poorawsanhsirk/Launch-Party-Badge-Software/assets/IMG_2383.JPG

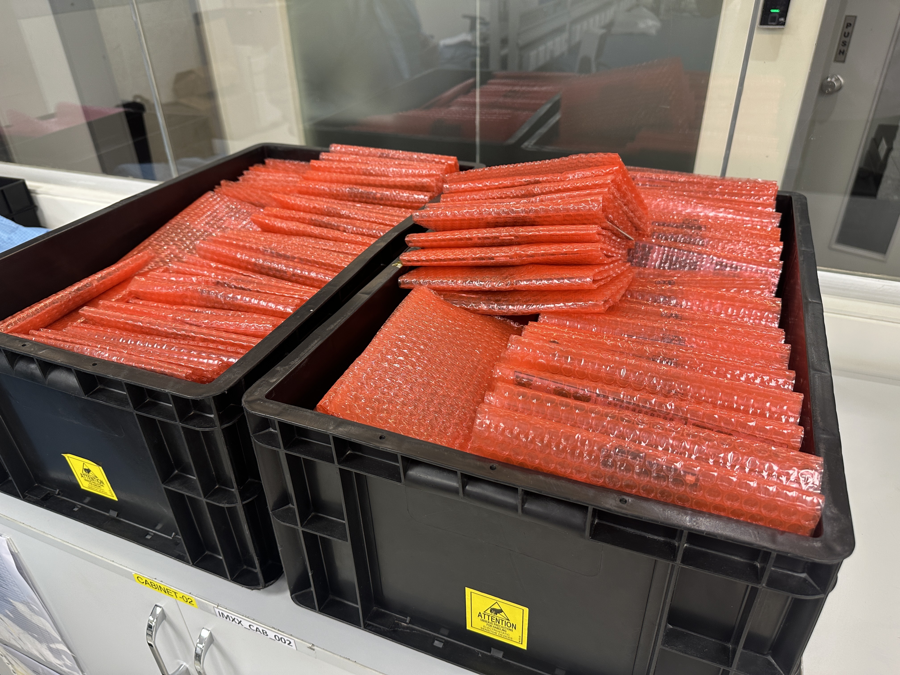
assets/IMG_2383.JPG
