poorawsanhsirk/Launch-Party-Badge-Software/assets/IMG_2390.JPG

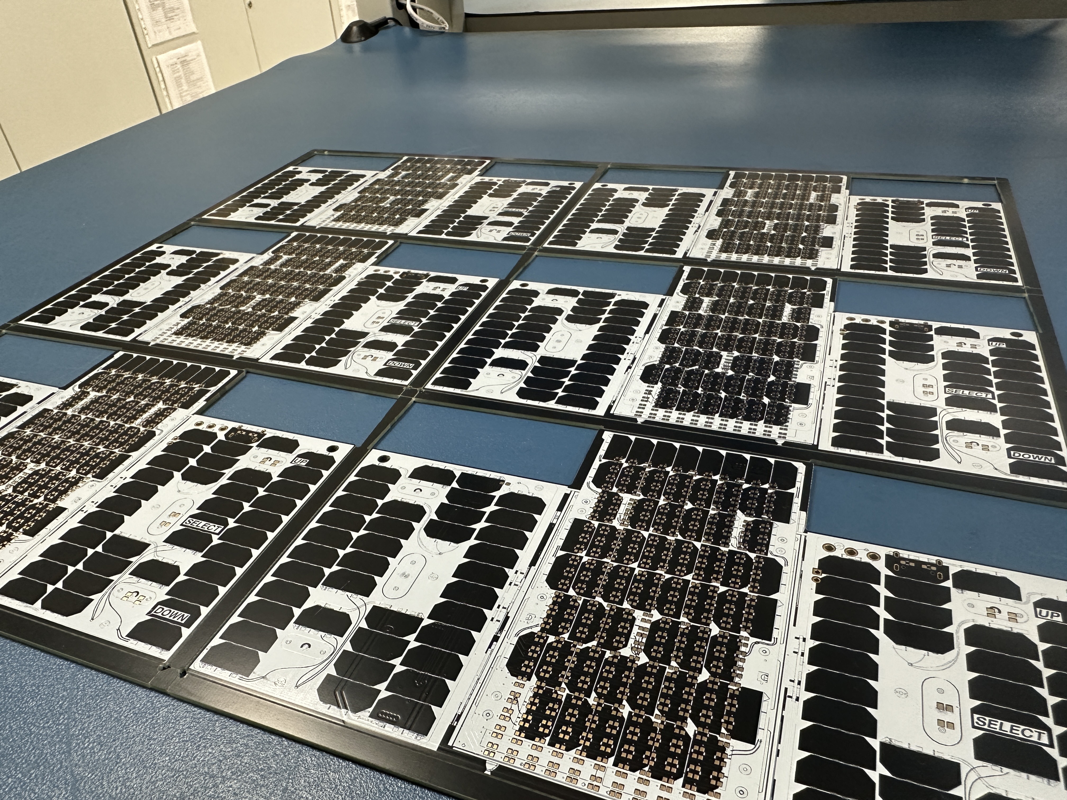
assets/IMG_2390.JPG
