poorawsanhsirk/Launch-Party-Badge-Software/hardware/FF1-LP-Badge/FF1-LP-Badge.kicad_sch

## KiCad design hardware/FF1-LP-Badge/FF1-LP-Badge.kicad_sch (2025-01-15)

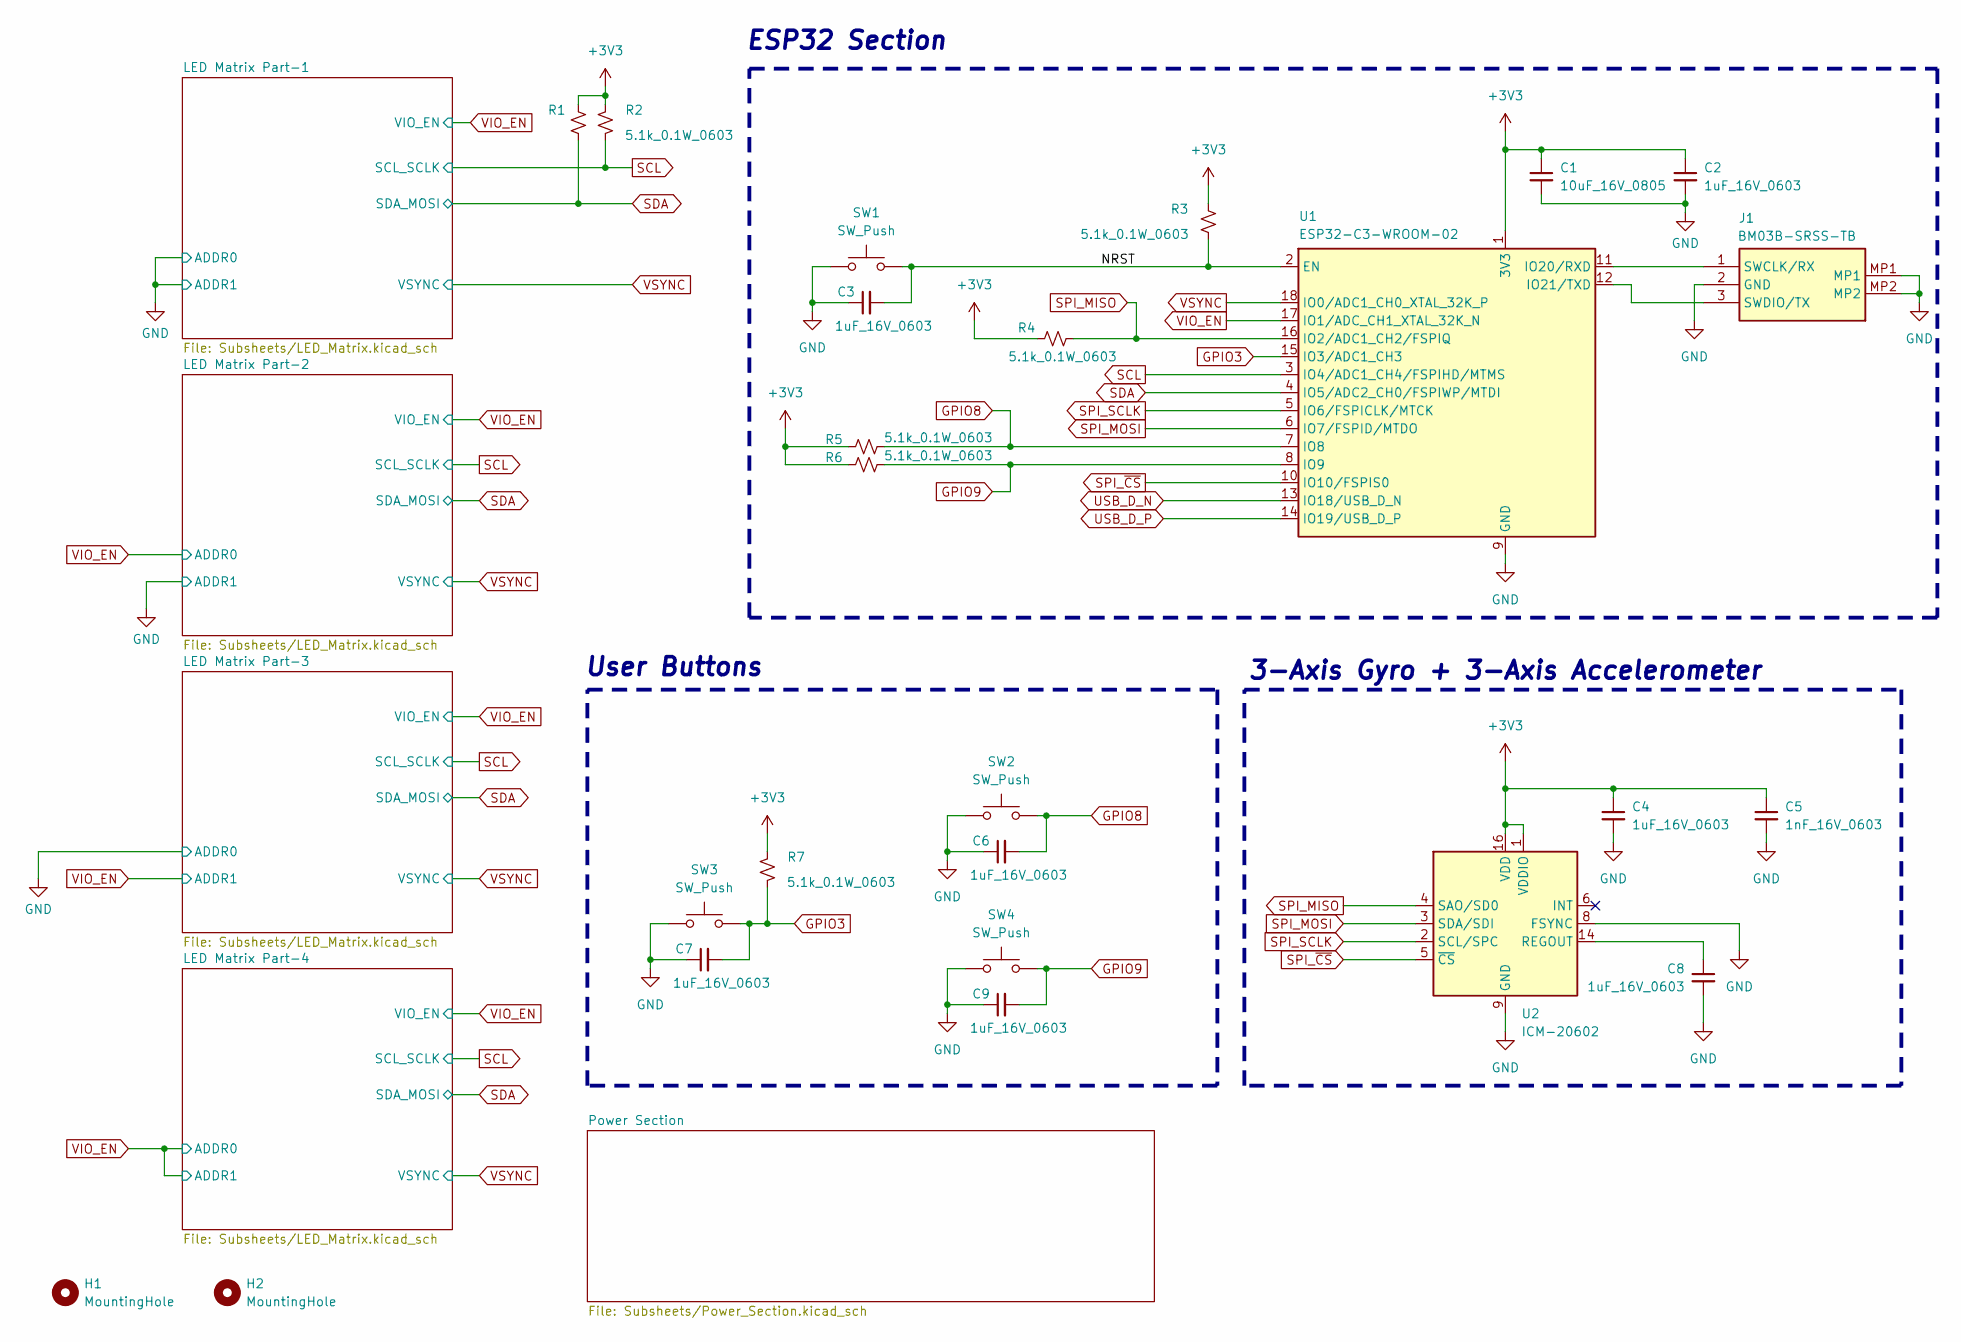
[picture p17: schematic FF1-LP-Badge.kicad_sch]

Parts:
C1: 10uF_16V_0805; C_0805_2012Metric_Pad1.18x1.45mm_HandSolder
C2, C3, C4, C6, C7, C8, C9: 1uF_16V_0603; C_0603_1608Metric_Pad1.08x0.95mm_HandSolder
C5: 1nF_16V_0603; C_0603_1608Metric_Pad1.08x0.95mm_HandSolder
H1, H2: MountingHole; MountingHole_3.2mm_M3
J1: BM03B-SRSS-TB; BM03BSRSSTB; Manufacturer_Part_Number BM03B-SRSS-TB; Mouser Part Number N/A
R1, R2, R3, R4, R5, R6, R7: 5.1k_0.1W_0603; R_0603_1608Metric_Pad0.98x0.95mm_HandSolder
SW1, SW2, SW3, SW4: SW_Push; Button-TSA008A187; Manufacturer Part Number TSA008A18726A07; LCSC C2888423
U1: ESP32-C3-WROOM-02; Manufacturer Part Number ESP32-C3-WROOM-02-N4; LCSC C2934560
U2: ICM-20602; LGA-16_3x3mm_P0.5mm_LayoutBorder3x5y; Manufacturer Part Number ICM-20602; LCSC C97633

Connections:
+3V3: C1.1, C2.1, C4.1, C5.1, R1.2, R2.2, R3.2, R4.2, R5.2, R6.2, R7.2, U1.1 (3V3), U2.1 (VDDIO), U2.16 (VDD)
GND: C1.2, C2.2, C3.1, C4.2, C5.2, C6.1, C7.1, C8.2, C9.1, J1.2 (GND), J1.MP1, J1.MP2, SW1.1, SW2.1, SW3.1, SW4.1, U1.9 (GND), U1.19 (GND), U2.8 (FSYNC), U2.9 (GND), U2.10 (GND), U2.11 (GND), U2.12 (GND), U2.13 (GND), U2.15 (GND)
GPIO3: C7.2, R7.1, SW3.2, U1.15 (IO3/ADC1_CH3)
GPIO8: C6.2, R5.1, SW2.2, U1.7 (IO8)
GPIO9: C9.2, R6.1, SW4.2, U1.8 (IO9)
NRST: C3.2, R3.1, SW1.2, U1.2 (EN)
unnamed: C8.1, U2.14 (REGOUT)
unnamed: J1.1 (SWCLK/RX), U1.11 (IO20/RXD)
unnamed: J1.3 (SWDIO/TX), U1.12 (IO21/TXD)
SCL: R2.1, U1.3 (IO4/ADC1_CH4/FSPIHD/MTMS)
SDA: R1.1, U1.4 (IO5/ADC2_CH0/FSPIWP/MTDI)
SPI_MISO: R4.1, U1.16 (IO2/ADC1_CH2/FSPIQ), U2.4 (SAO/SD0)
SPI_MOSI: U1.6 (IO7/FSPID/MTDO), U2.3 (SDA/SDI)
SPI_SCLK: U1.5 (IO6/FSPICLK/MTCK), U2.2 (SCL/SPC)
SPI_~CS: U1.10 (IO10/FSPIS0), U2.5 (~CS)
USB_D_N: U1.13 (IO18/USB_D_N)
USB_D_P: U1.14 (IO19/USB_D_P)
VIO_EN: U1.17 (IO1/ADC_CH1_XTAL_32K_N)
VSYNC: U1.18 (IO0/ADC1_CH0_XTAL_32K_P)

Notes on the sheet:
ESP32 Section
User Buttons
3-Axis Gyro + 3-Axis Accelerometer
