poorawsanhsirk/Launch-Party-Badge-Software/hardware/FF1-LP-Badge/Subsheets/LED_Matrix.kicad_sch

## KiCad design hardware/FF1-LP-Badge/Subsheets/LED_Matrix.kicad_sch (2025-01-15)

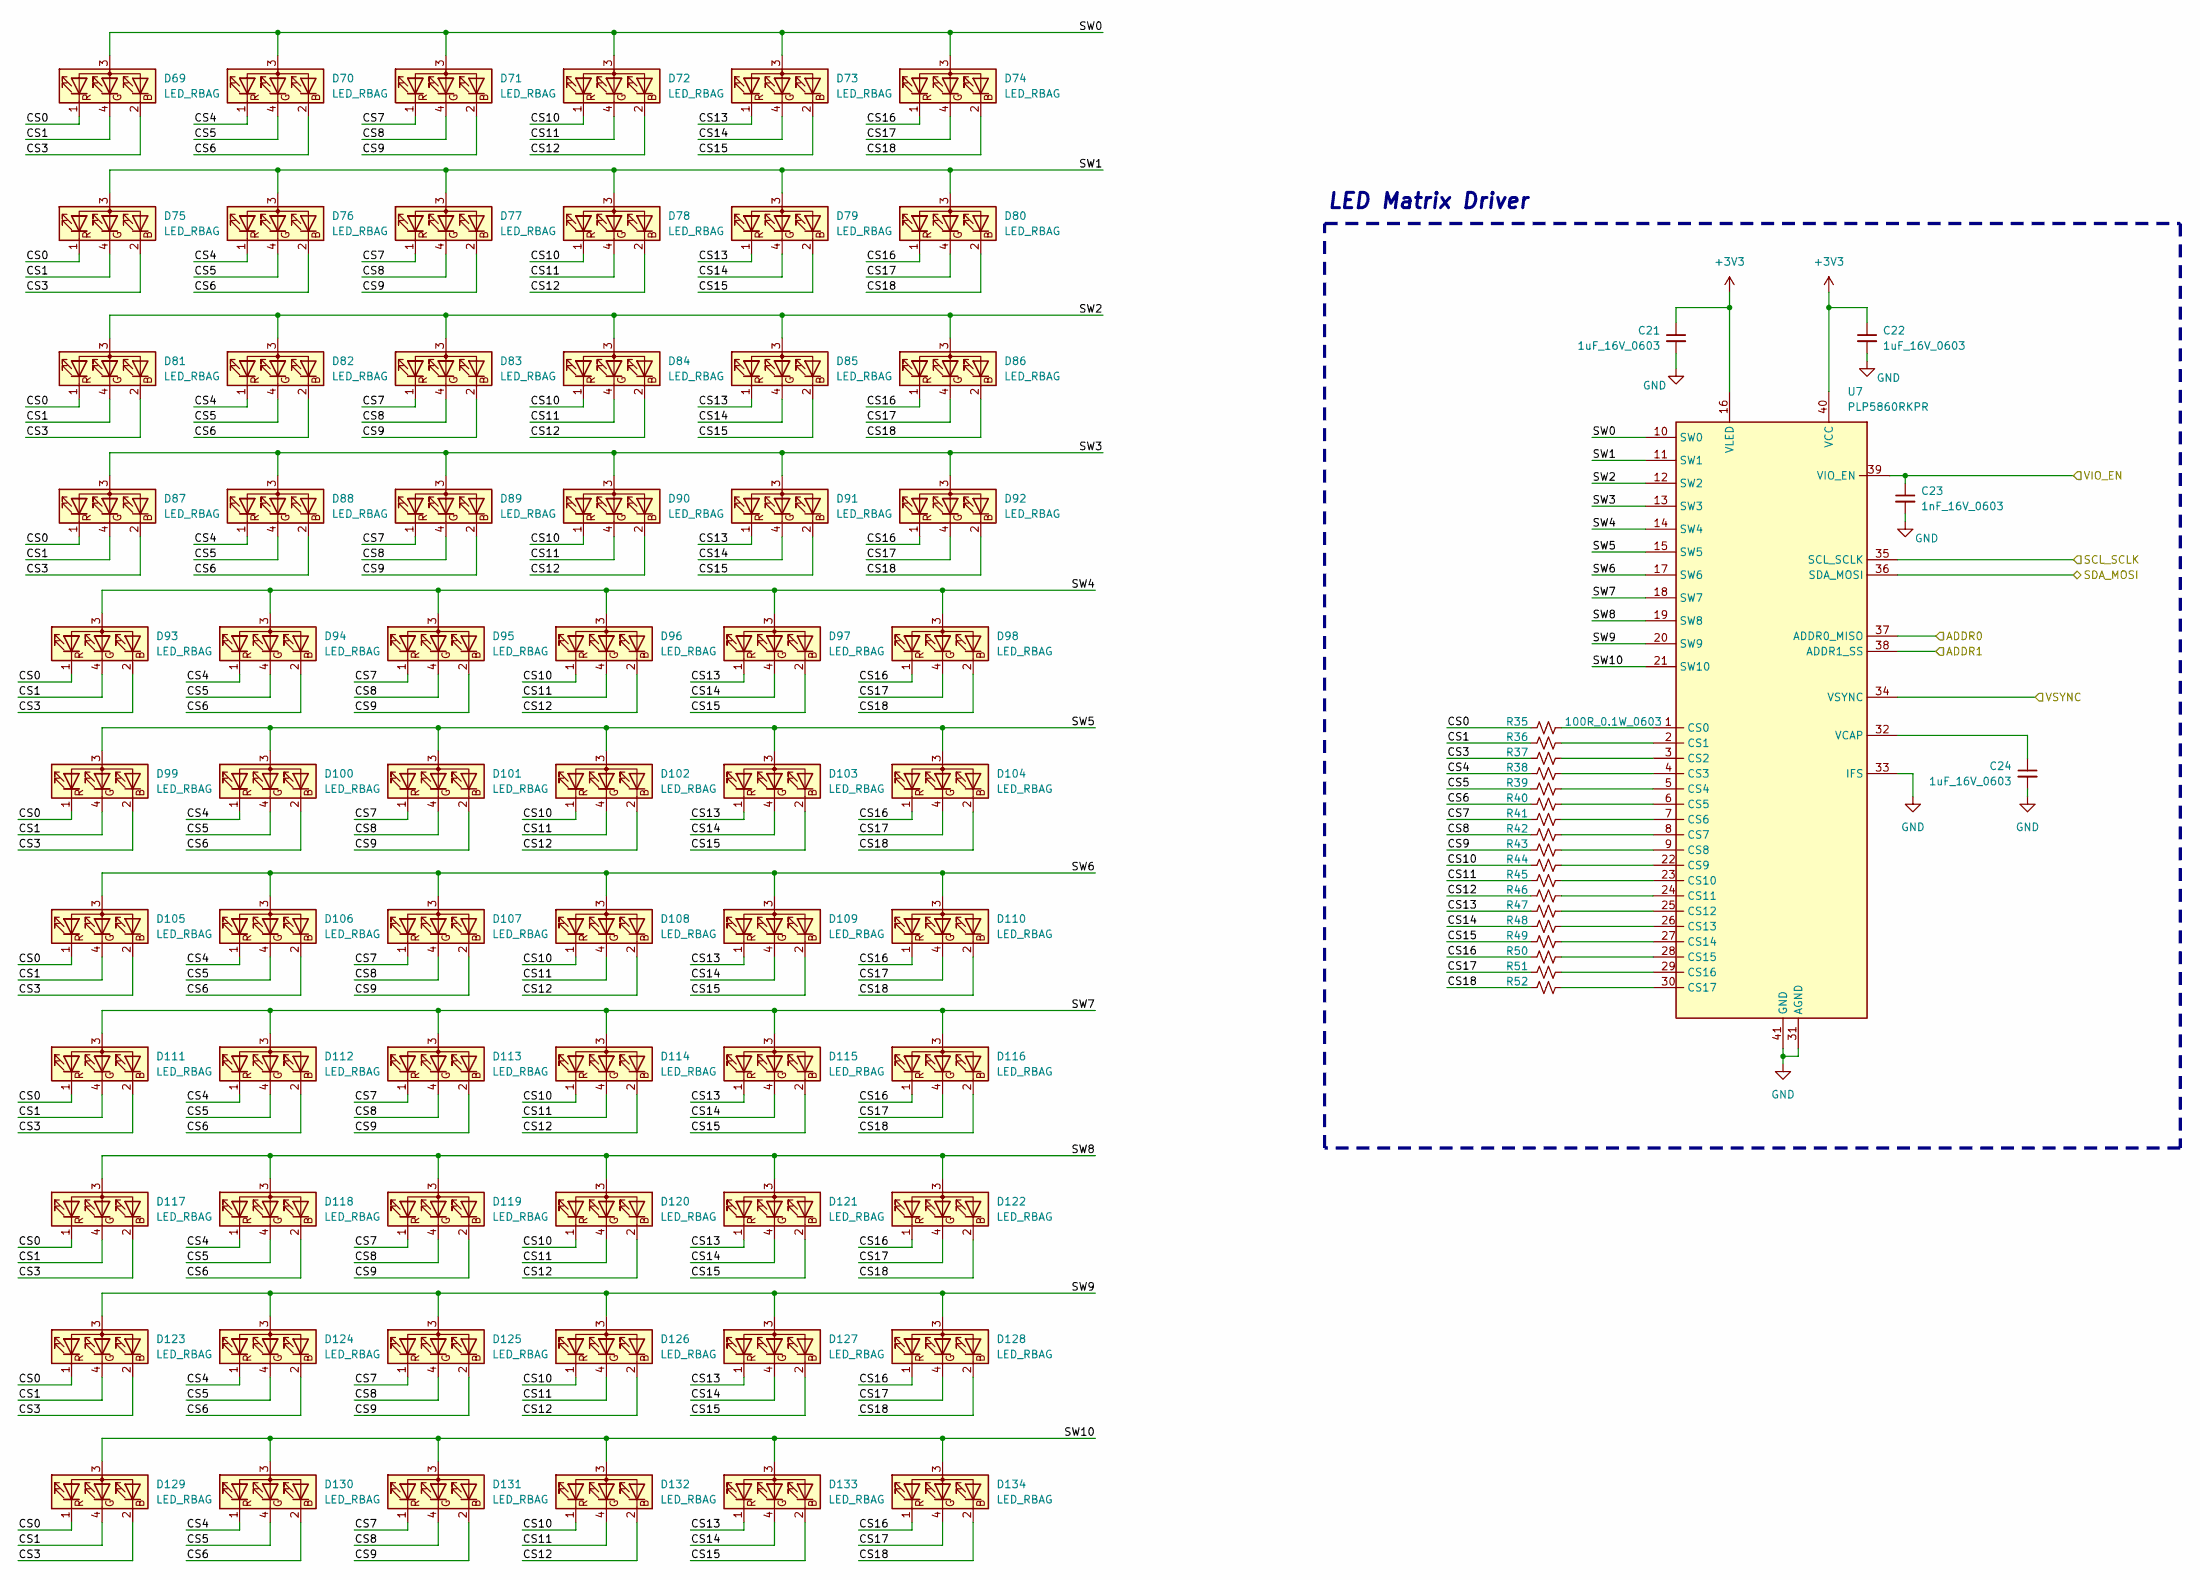
[picture p18: schematic LED_Matrix.kicad_sch]

Parts:
C21, C22, C24: 1uF_16V_0603; C_0603_1608Metric_Pad1.08x0.95mm_HandSolder
C23: 1nF_16V_0603; C_0603_1608Metric_Pad1.08x0.95mm_HandSolder
D69, D70, D71, D72, D73, D74, D75, D76, D77, D78, D79, D80, D81, D82, D83, D84, D85, D86, D87, D88, D89, D90, D91, D92, D93, D94, D95, D96, D97, D98, D99, D100, D101, D102, D103, D104, D105, D106, D107, D108, D109, D110, D111, D112, D113, D114, D115, D116, D117, D118, D119, D120, D121, D122, D123, D124, D125, D126, D127, D128, D129, D130, D131, D132, D133, D134: LED_RBAG; NHB2020RGBAHF; Manufacturer Part Number NH-B2020RGBA-HF; LCSC C2874116
R35, R36, R37, R38, R39, R40, R41, R42, R43, R44, R45, R46, R47, R48, R49, R50, R51, R52: 100R_0.1W_0603; R_0603_1608Metric_Pad0.98x0.95mm_HandSolder
U7: PLP5860RKPR; QFN40P500X500X100-41N-D; Manufacturer_Part_Number PLP5860RKPR

Connections:
+3V3: C21.1, C22.1, U7.16 (VLED), U7.40 (VCC)
ADDR0: U7.37 (ADDR0_MISO)
ADDR1: U7.38 (ADDR1_SS)
CS0: D69.1 (RK), D75.1 (RK), D81.1 (RK), D87.1 (RK), D93.1 (RK), D99.1 (RK), D105.1 (RK), D111.1 (RK), D117.1 (RK), D123.1 (RK), D129.1 (RK), R35.1
CS1: D69.4 (GK), D75.4 (GK), D81.4 (GK), D87.4 (GK), D93.4 (GK), D99.4 (GK), D105.4 (GK), D111.4 (GK), D117.4 (GK), D123.4 (GK), D129.4 (GK), R36.1
CS3: D69.2 (BK), D75.2 (BK), D81.2 (BK), D87.2 (BK), D93.2 (BK), D99.2 (BK), D105.2 (BK), D111.2 (BK), D117.2 (BK), D123.2 (BK), D129.2 (BK), R37.1
CS4: D70.1 (RK), D76.1 (RK), D82.1 (RK), D88.1 (RK), D94.1 (RK), D100.1 (RK), D106.1 (RK), D112.1 (RK), D118.1 (RK), D124.1 (RK), D130.1 (RK), R38.1
CS5: D70.4 (GK), D76.4 (GK), D82.4 (GK), D88.4 (GK), D94.4 (GK), D100.4 (GK), D106.4 (GK), D112.4 (GK), D118.4 (GK), D124.4 (GK), D130.4 (GK), R39.1
CS6: D70.2 (BK), D76.2 (BK), D82.2 (BK), D88.2 (BK), D94.2 (BK), D100.2 (BK), D106.2 (BK), D112.2 (BK), D118.2 (BK), D124.2 (BK), D130.2 (BK), R40.1
CS7: D71.1 (RK), D77.1 (RK), D83.1 (RK), D89.1 (RK), D95.1 (RK), D101.1 (RK), D107.1 (RK), D113.1 (RK), D119.1 (RK), D125.1 (RK), D131.1 (RK), R41.1
CS8: D71.4 (GK), D77.4 (GK), D83.4 (GK), D89.4 (GK), D95.4 (GK), D101.4 (GK), D107.4 (GK), D113.4 (GK), D119.4 (GK), D125.4 (GK), D131.4 (GK), R42.1
CS9: D71.2 (BK), D77.2 (BK), D83.2 (BK), D89.2 (BK), D95.2 (BK), D101.2 (BK), D107.2 (BK), D113.2 (BK), D119.2 (BK), D125.2 (BK), D131.2 (BK), R43.1
CS10: D72.1 (RK), D78.1 (RK), D84.1 (RK), D90.1 (RK), D96.1 (RK), D102.1 (RK), D108.1 (RK), D114.1 (RK), D120.1 (RK), D126.1 (RK), D132.1 (RK), R44.1
CS11: D72.4 (GK), D78.4 (GK), D84.4 (GK), D90.4 (GK), D96.4 (GK), D102.4 (GK), D108.4 (GK), D114.4 (GK), D120.4 (GK), D126.4 (GK), D132.4 (GK), R45.1
CS12: D72.2 (BK), D78.2 (BK), D84.2 (BK), D90.2 (BK), D96.2 (BK), D102.2 (BK), D108.2 (BK), D114.2 (BK), D120.2 (BK), D126.2 (BK), D132.2 (BK), R46.1
CS13: D73.1 (RK), D79.1 (RK), D85.1 (RK), D91.1 (RK), D97.1 (RK), D103.1 (RK), D109.1 (RK), D115.1 (RK), D121.1 (RK), D127.1 (RK), D133.1 (RK), R47.1
CS14: D73.4 (GK), D79.4 (GK), D85.4 (GK), D91.4 (GK), D97.4 (GK), D103.4 (GK), D109.4 (GK), D115.4 (GK), D121.4 (GK), D127.4 (GK), D133.4 (GK), R48.1
CS15: D73.2 (BK), D79.2 (BK), D85.2 (BK), D91.2 (BK), D97.2 (BK), D103.2 (BK), D109.2 (BK), D115.2 (BK), D121.2 (BK), D127.2 (BK), D133.2 (BK), R49.1
CS16: D74.1 (RK), D80.1 (RK), D86.1 (RK), D92.1 (RK), D98.1 (RK), D104.1 (RK), D110.1 (RK), D116.1 (RK), D122.1 (RK), D128.1 (RK), D134.1 (RK), R50.1
CS17: D74.4 (GK), D80.4 (GK), D86.4 (GK), D92.4 (GK), D98.4 (GK), D104.4 (GK), D110.4 (GK), D116.4 (GK), D122.4 (GK), D128.4 (GK), D134.4 (GK), R51.1
CS18: D74.2 (BK), D80.2 (BK), D86.2 (BK), D92.2 (BK), D98.2 (BK), D104.2 (BK), D110.2 (BK), D116.2 (BK), D122.2 (BK), D128.2 (BK), D134.2 (BK), R52.1
GND: C21.2, C22.2, C23.2, C24.2, U7.31 (AGND), U7.33 (IFS), U7.41 (GND)
unnamed: C24.1, U7.32 (VCAP)
unnamed: R35.2, U7.1 (CS0)
unnamed: R36.2, U7.2 (CS1)
unnamed: R37.2, U7.3 (CS2)
unnamed: R38.2, U7.4 (CS3)
unnamed: R39.2, U7.5 (CS4)
unnamed: R40.2, U7.6 (CS5)
unnamed: R41.2, U7.7 (CS6)
unnamed: R42.2, U7.8 (CS7)
unnamed: R43.2, U7.9 (CS8)
unnamed: R44.2, U7.22 (CS9)
unnamed: R45.2, U7.23 (CS10)
unnamed: R46.2, U7.24 (CS11)
unnamed: R47.2, U7.25 (CS12)
unnamed: R48.2, U7.26 (CS13)
unnamed: R49.2, U7.27 (CS14)
unnamed: R50.2, U7.28 (CS15)
unnamed: R51.2, U7.29 (CS16)
unnamed: R52.2, U7.30 (CS17)
SCL_SCLK: U7.35 (SCL_SCLK)
SDA_MOSI: U7.36 (SDA_MOSI)
SW0: D69.3 (A), D70.3 (A), D71.3 (A), D72.3 (A), D73.3 (A), D74.3 (A), U7.10 (SW0)
SW1: D75.3 (A), D76.3 (A), D77.3 (A), D78.3 (A), D79.3 (A), D80.3 (A), U7.11 (SW1)
SW2: D81.3 (A), D82.3 (A), D83.3 (A), D84.3 (A), D85.3 (A), D86.3 (A), U7.12 (SW2)
SW3: D87.3 (A), D88.3 (A), D89.3 (A), D90.3 (A), D91.3 (A), D92.3 (A), U7.13 (SW3)
SW4: D93.3 (A), D94.3 (A), D95.3 (A), D96.3 (A), D97.3 (A), D98.3 (A), U7.14 (SW4)
SW5: D99.3 (A), D100.3 (A), D101.3 (A), D102.3 (A), D103.3 (A), D104.3 (A), U7.15 (SW5)
SW6: D105.3 (A), D106.3 (A), D107.3 (A), D108.3 (A), D109.3 (A), D110.3 (A), U7.17 (SW6)
SW7: D111.3 (A), D112.3 (A), D113.3 (A), D114.3 (A), D115.3 (A), D116.3 (A), U7.18 (SW7)
SW8: D117.3 (A), D118.3 (A), D119.3 (A), D120.3 (A), D121.3 (A), D122.3 (A), U7.19 (SW8)
SW9: D123.3 (A), D124.3 (A), D125.3 (A), D126.3 (A), D127.3 (A), D128.3 (A), U7.20 (SW9)
SW10: D129.3 (A), D130.3 (A), D131.3 (A), D132.3 (A), D133.3 (A), D134.3 (A), U7.21 (SW10)
VIO_EN: C23.1, U7.39 (VIO_EN)
VSYNC: U7.34 (VSYNC)

Notes on the sheet:
LED Matrix Driver
