poorawsanhsirk/Launch-Party-Badge-Software/hardware/FF1-LP-Badge/Subsheets/Power_Section.kicad_sch

## KiCad design hardware/FF1-LP-Badge/Subsheets/Power_Section.kicad_sch (2025-01-15)

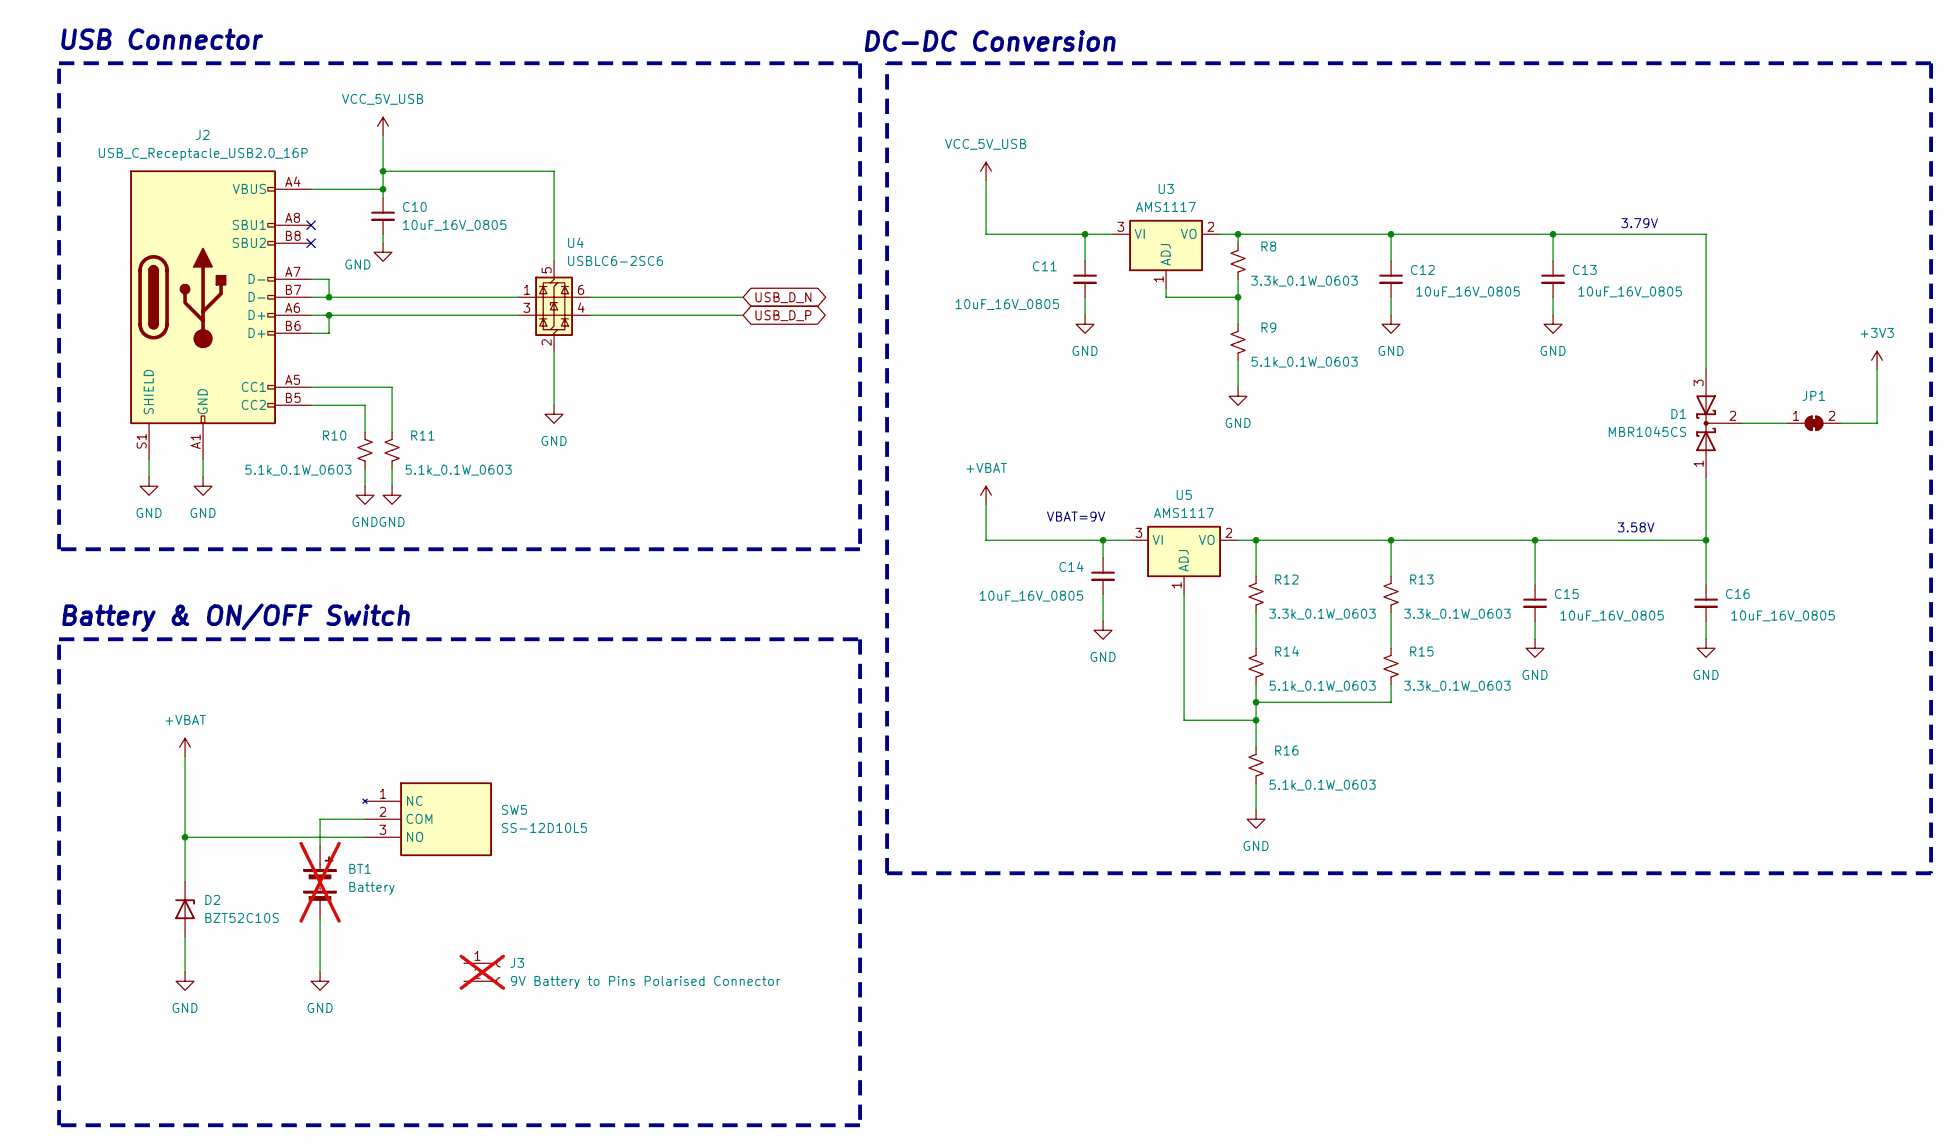
[picture p19: schematic Power_Section.kicad_sch]

Parts:
BT1: Battery; PinHeader_1x02_P2.54mm_Vertical; not fitted
C10, C11, C12, C13, C14, C15, C16: 10uF_16V_0805; C_0805_2012Metric_Pad1.18x1.45mm_HandSolder
D1: MBR1045CS; TO-252-3_TabPin2; Manufacturer Part Number MBR1045CS; LCSC C2898534
D2: BZT52C10S; D_SOD-323_HandSoldering; Manufacturer Part Number BZT52C10S; LCSC C571388
J2: USB_C_Receptacle_USB2.0_16P; USB_C_Receptacle_GCT_USB4105-xx-A_16P_TopMnt_Horizontal; Manufacturer Part Number KH-TYPE-C-16P; LCSC C709357
J3: 9V Battery to Pins Polarised Connector; not fitted
JP1: SolderJumper_2_Open; SolderJumper-2_P1.3mm_Bridged2Bar_RoundedPad1.0x1.5mm
R8, R12, R13, R15: 3.3k_0.1W_0603; R_0603_1608Metric_Pad0.98x0.95mm_HandSolder
R9, R10, R11, R14, R16: 5.1k_0.1W_0603; R_0603_1608Metric_Pad0.98x0.95mm_HandSolder
SW5: SS-12D10L5; SS12D10L5; Manufacturer Part Number SS-12D10L5; LCSC C319012
U3, U5: AMS1117; SOT-223-3_TabPin2; Manufacturer Part Number AMS1117-ADJ; LCSC C347224
U4: USBLC6-2SC6; SOT-23-6; Manufacturer Part Number USBLC6-2SC6; LCSC C7519

Connections:
+3V3: JP1.2 (B)
+VBAT: C14.1, D2.1 (K), SW5.3 (NO), U5.3 (VI)
GND: BT1.2 (-), C10.2, C11.2, C12.2, C13.2, C14.2, C15.2, C16.2, D2.2 (A), J2.A1 (GND), J2.A12 (GND), J2.B1 (GND), J2.B12 (GND), J2.S1 (SHIELD), R9.2, R10.2, R11.2, R16.2, U4.2 (GND)
unnamed: BT1.1 (+), SW5.2 (COM)
unnamed: C12.1, C13.1, D1.3 (A), R8.1, U3.2 (VO)
unnamed: C15.1, C16.1, D1.1 (A), R12.1, R13.1, U5.2 (VO)
unnamed: D1.2 (K), JP1.1 (A)
unnamed: J2.A5 (CC1), R11.1
unnamed: J2.A6 (D+), J2.B6 (D+), U4.3 (I/O2)
unnamed: J2.A7 (D-), J2.B7 (D-), U4.1 (I/O1)
unnamed: J2.B5 (CC2), R10.1
unnamed: R8.2, R9.1, U3.1 (ADJ)
unnamed: R12.2, R14.1
unnamed: R13.2, R15.1
unnamed: R14.2, R15.2, R16.1, U5.1 (ADJ)
USB_D_N: U4.6 (I/O1)
USB_D_P: U4.4 (I/O2)
VCC_5V_USB: C10.1, C11.1, J2.A4 (VBUS), J2.A9 (VBUS), J2.B4 (VBUS), J2.B9 (VBUS), U3.3 (VI), U4.5 (VBUS)

Notes on the sheet:
DC-DC Conversion
3.79V
USB Connector
Battery & ON/OFF Switch
3.58V
VBAT=9V
